larspontoppidan/midimixfix/HW/Misc/foot_pedal_cct_new.GIF

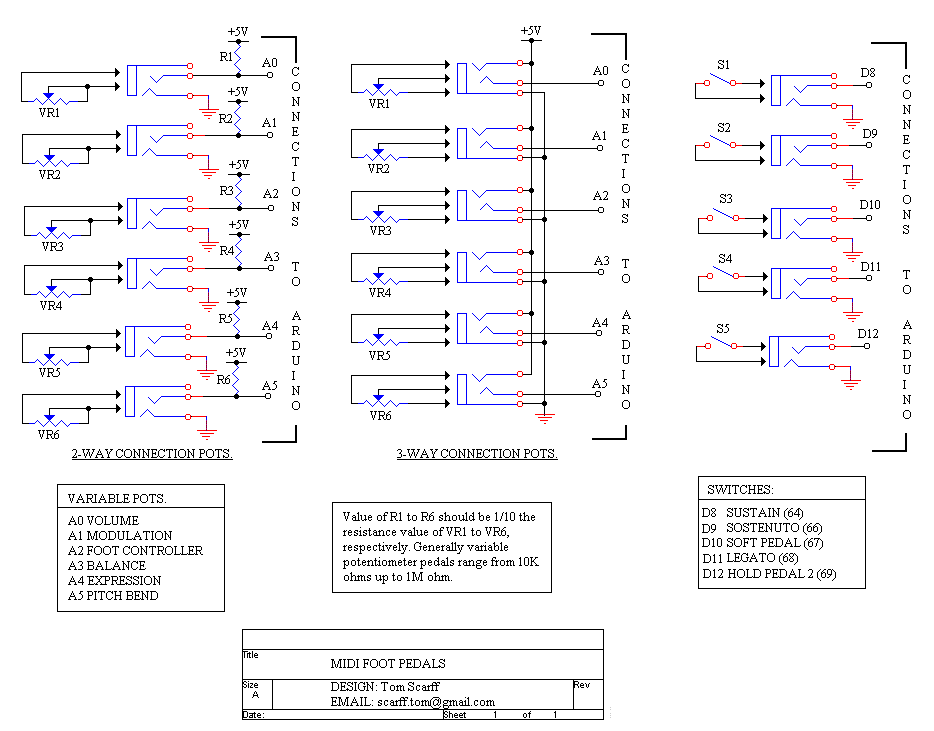
HW/Misc/foot_pedal_cct_new.GIF
