larspontoppidan/midimixfix/Releases/HW Release Rev 1/Pictures/Midimixfix mounted.JPG

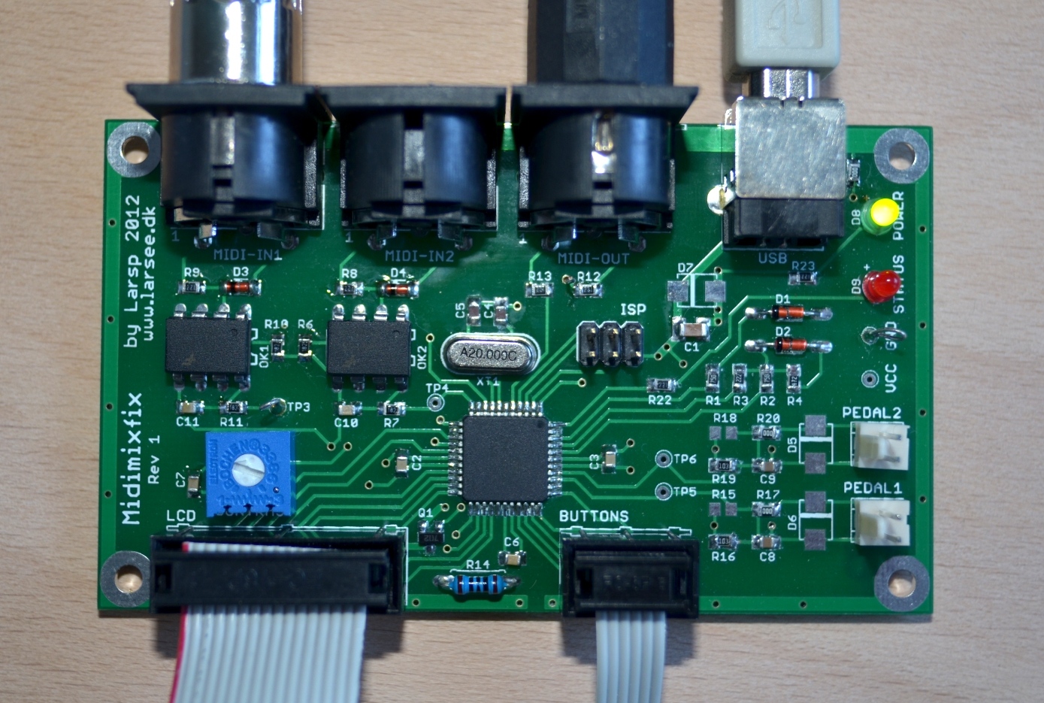
Releases/HW Release Rev 1/Pictures/Midimixfix mounted.JPG
