larspontoppidan/midimixfix/Releases/HW Release Rev 1/Pictures/Midimixfix PCB Back.JPG

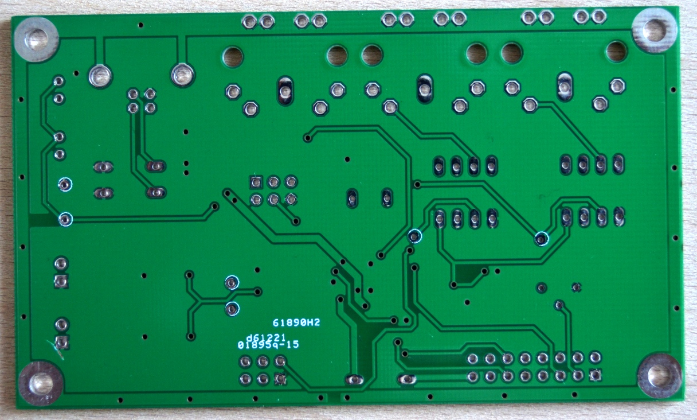
Releases/HW Release Rev 1/Pictures/Midimixfix PCB Back.JPG
