larspontoppidan/midimixfix/Releases/HW Release Rev 1/Pictures/Midimixfix PCB Front.JPG

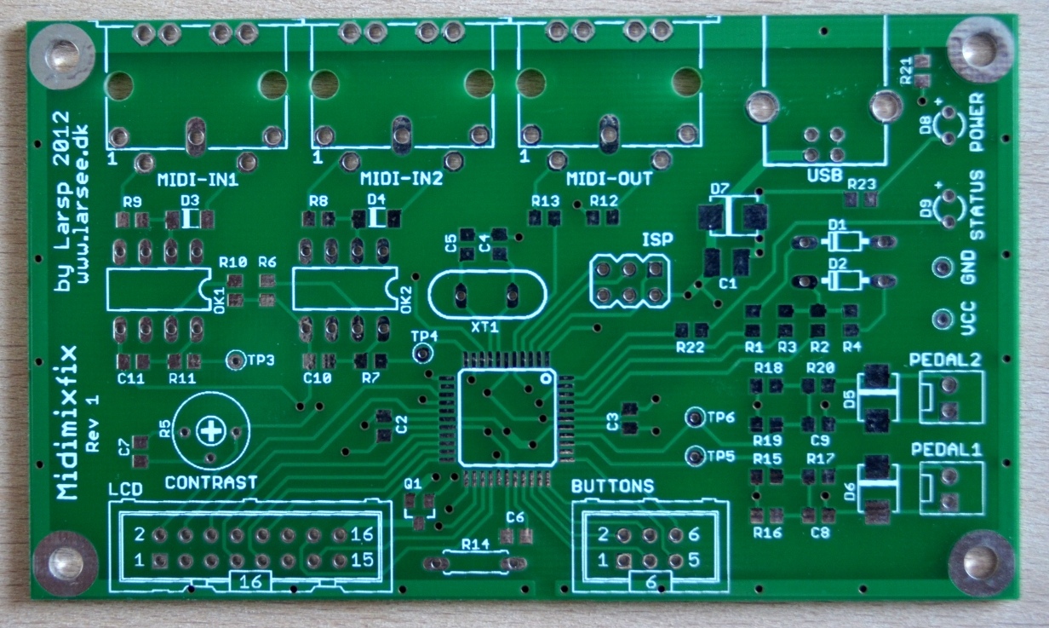
Releases/HW Release Rev 1/Pictures/Midimixfix PCB Front.JPG
