larspontoppidan/midimixfix/Releases/HW Release Rev 1/Pictures/Midimixfix prototype.JPG

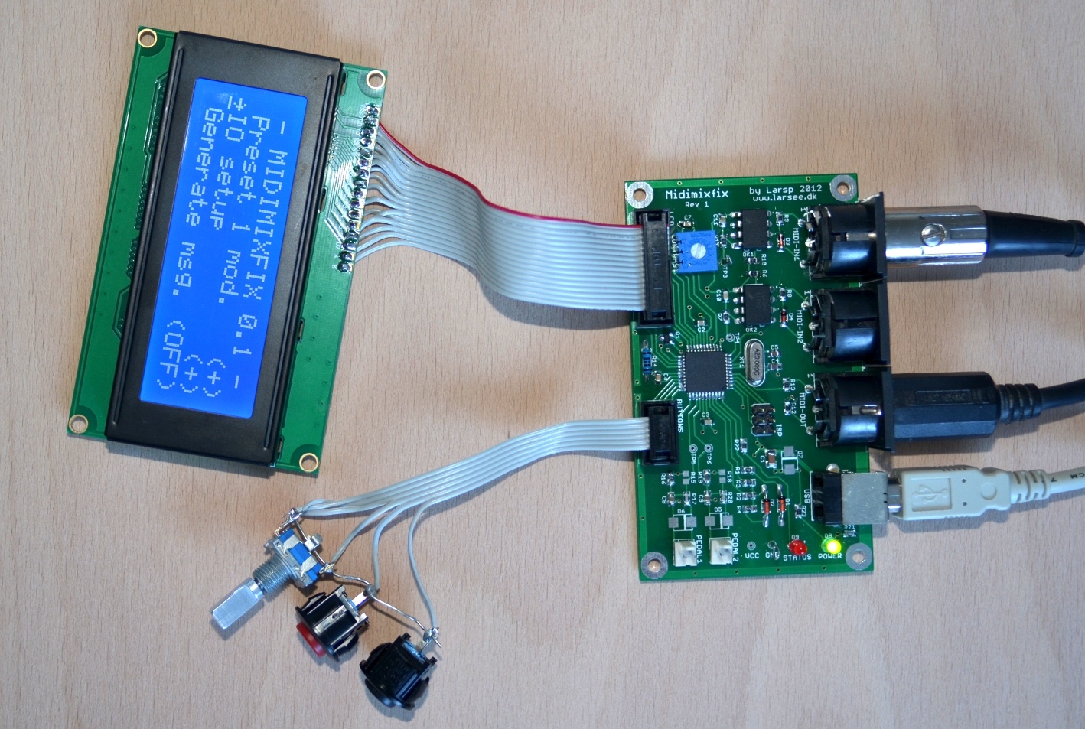
Releases/HW Release Rev 1/Pictures/Midimixfix prototype.JPG
