larspontoppidan/midimixfix/HW/Components/JACK receptacle/B1.JPG

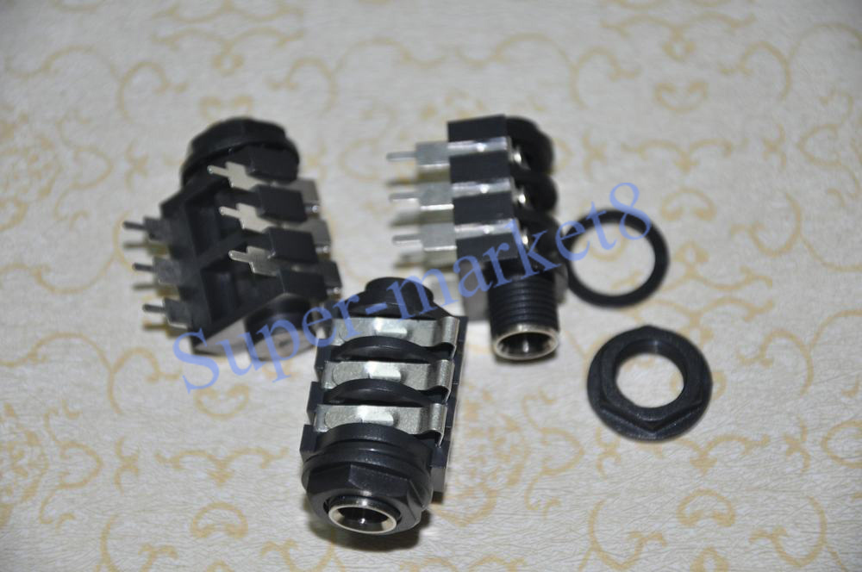
HW/Components/JACK receptacle/B1.JPG
