larspontoppidan/midimixfix/HW/Components/LCD Module/2004-lcd-module.jpg

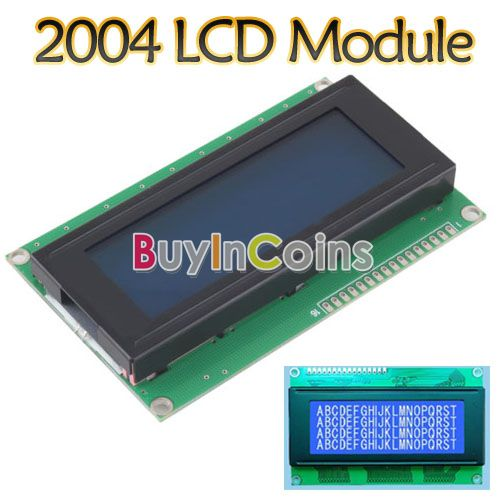
HW/Components/LCD Module/2004-lcd-module.jpg
