larspontoppidan/midimixfix/HW/Components/LCD Module/2004-lcd-module_03.jpg

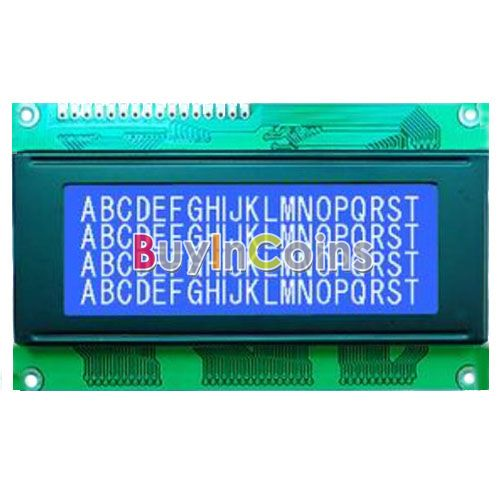
HW/Components/LCD Module/2004-lcd-module_03.jpg
