larspontoppidan/midimixfix/HW/Components/LCD Module/2004-lcd-module_05.jpg

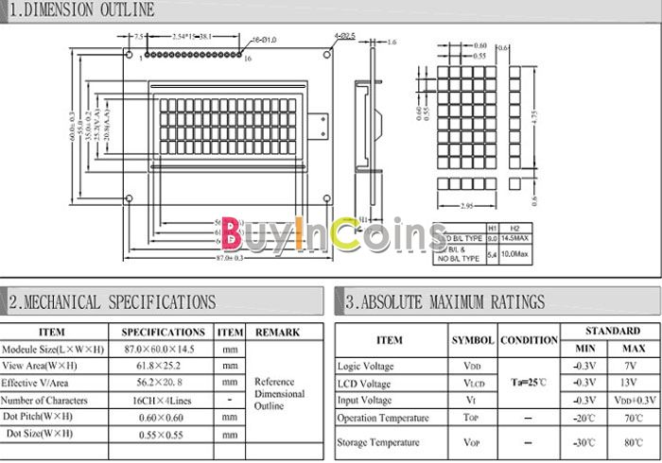
HW/Components/LCD Module/2004-lcd-module_05.jpg
