larspontoppidan/midimixfix/HW/Components/Rotary encoder/14002056_1_image_59740.jpg

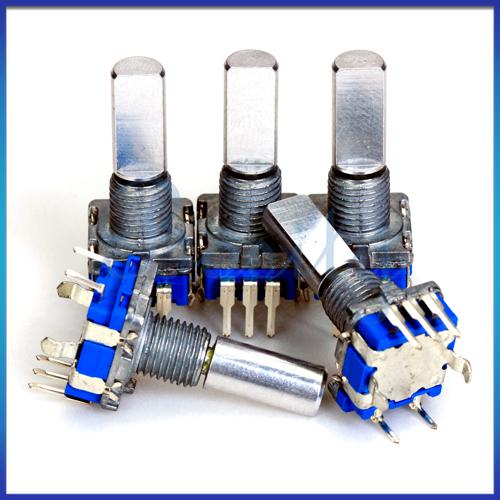
HW/Components/Rotary encoder/14002056_1_image_59740.jpg
