larspontoppidan/midimixfix/Releases/HW Release Rev 1/Cable assembly/Midimixfix_into_box_012-1024x678.jpg

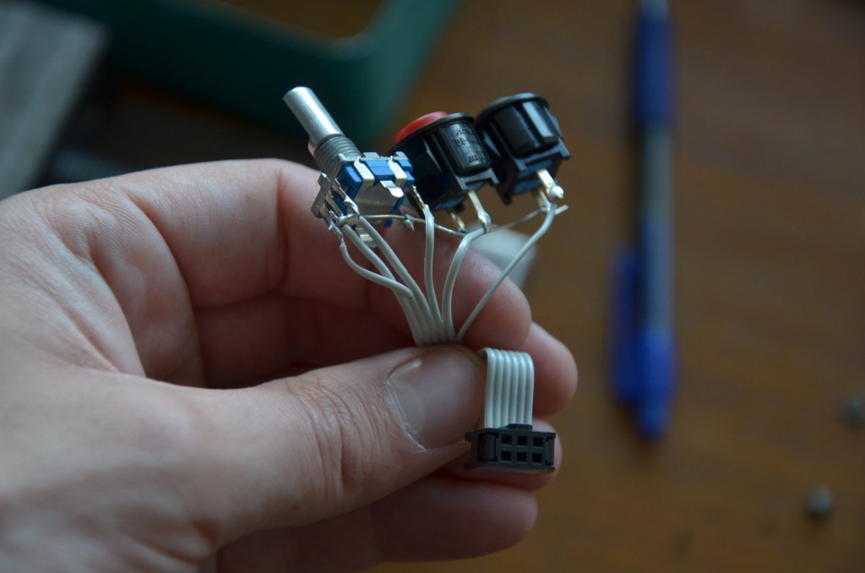
Releases/HW Release Rev 1/Cable assembly/Midimixfix_into_box_012-1024x678.jpg
