larspontoppidan/midimixfix/SW/src/Filters/controlnoteon.h

/*
 * controlnoteon.h
 *
 *  Created on: May 16, 2014
 *      Author: lars
 */

#ifndef CONTROLNOTEON_H_
#define CONTROLNOTEON_H_



#include "../common.h"
#include "../filterinterface.h"
#include <avr/pgmspace.h>

extern const filterInterface_t PROGMEM ccnoteon_Filter;



#endif /* CONTROLNOTEON_H_ */
