larspontoppidan/midimixfix/SW/src/Filters/modifycontroller.h

/*
 * modifycontroller.h
 *
 *  Created on: Oct 18, 2013
 *      Author: lars
 */

#ifndef MODIFYCONTROLLER_H_
#define MODIFYCONTROLLER_H_


#include "../common.h"
#include "../filterinterface.h"
#include <avr/pgmspace.h>

extern const filterInterface_t PROGMEM modifycc_Filter;


#endif /* MODIFYCONTROLLER_H_ */
