larspontoppidan/midimixfix/SW/src/Filters/pedals.c

//
// Filename    : pedals.c
// Code module : Generation of midi messages from pedal readings for MidiMixFix
// Project     : Midimixfix
// URL         : http://larsee.dk
//
// --------------------------------  LICENSE  -----------------------------------
//
// Copyright (c) 2013, Lars Ole Pontoppidan (Larsp)
// All rights reserved.
//
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
// THIS SOFTWARE IS PROVIDED BY THE COPYRIGHT HOLDERS AND CONTRIBUTORS "AS IS" AND
// ANY EXPRESS OR IMPLIED WARRANTIES, INCLUDING, BUT NOT LIMITED TO, THE IMPLIED
// WARRANTIES OF MERCHANTABILITY AND FITNESS FOR A PARTICULAR PURPOSE ARE
// DISCLAIMED. IN NO EVENT SHALL THE COPYRIGHT OWNER OR CONTRIBUTORS BE LIABLE FOR
// ANY DIRECT, INDIRECT, INCIDENTAL, SPECIAL, EXEMPLARY, OR CONSEQUENTIAL DAMAGES
// (INCLUDING, BUT NOT LIMITED TO, PROCUREMENT OF SUBSTITUTE GOODS OR SERVICES;
// LOSS OF USE, DATA, OR PROFITS; OR BUSINESS INTERRUPTION) HOWEVER CAUSED AND
// ON ANY THEORY OF LIABILITY, WHETHER IN CONTRACT, STRICT LIABILITY, OR TORT
// (INCLUDING NEGLIGENCE OR OTHERWISE) ARISING IN ANY WAY OUT OF THE USE OF THIS
// SOFTWARE, EVEN IF ADVISED OF THE POSSIBILITY OF SUCH DAMAGE.
//
//
//
// ------------------------------  DESCRIPTION  ---------------------------------


// -------------------------------  INCLUDES  -----------------------------------
/*
 * pedals.c
 *
 *  Created on: May 11, 2013
 *      Author: lars
 */


#include "../common.h"
#include "../midimessage.h"
#include "../midigenerics.h"
#include "../midiprocessing.h"
#include "../errors.h"
#include "../util.h"
#include "../hal.h"
#include "../filters.h"
#include "../ui.h"
#include "../menus/filtermenu.h"
#include <avr/pgmspace.h>
#include "filteruids.h"

// DATA PROCESSING
//
// A variable pedal is sampled by midimixfix using a voltage divider into a 10-bit ADC:
//
//   VCC ---+
//          |
//         10k
//          |
//          +----  ADC
//          |
//       R_pedal
//          |
//   GND ---+
//
// The circuit maps the pedal resistance non-linearly to the voltage seen by the ADC:
//
//   V_ADC = VCC * R_pedal / (10k + R_pedal)
//
// If we want to derive the actual R_pedal value without the non-linearity, we need to find:
//
//   R_pedal = 10 * V_ADC / (VCC - V_ADC)
//
// To calculate R_pedal using above formula, a look up table is used. The table simply has
// one 16-bit entry for each possible ADC value, and is scaled to have unit 1/64 ohms.
// The scaling is selected to enable a convenient gain calculation followed by >> 8.
//
// Python to generate the table:
//
// from numpy import *
//
// a = range(1024)
//
// for i in xrange(1000):
//   a[i] = int(round(10000.0 / 64.0 * (i/1024.0) / (1.0-(i/1024.0))))
//
// array(a).reshape(-1,8)


// ------------------------------  PROTOTYPES  ----------------------------------


static uint8_t ProcessAdcValue(int8_t offset, uint8_t gain, uint16_t adc_value);
static uint8_t handleDigitalPedal_ISR(uint8_t p);
static uint8_t handleAnalogPedal_ISR(uint8_t p);

static uint8_t pedals_In1Create(uint8_t filter_step);
static uint8_t pedals_In2Create(uint8_t filter_step);
static void pedals_Destroy(uint8_t instance);
static void pedals_SetFilterStep(uint8_t instance, uint8_t filter_step);
static void pedals_LoadConfig(uint8_t instance, void* data);
static void pedals_SaveConfig(uint8_t instance, void* data);
static uint8_t pedals_ProcessMidiMsgNull(uint8_t instance, midiMsg_t *msg);
static void pedals_WriteMenuText(uint8_t instance, uint8_t menu_item, void *dest);
static void pedals_HandleUiEvent(uint8_t instance, uint8_t menu_item, uint8_t ui_event);

// --------------------------  TYPES AND CONSTANTS  -----------------------------

#define GAIN_USE_DIGITAL      0

#define USE_MIDI_CHANNEL 0

#define DIGITAL_HIGH_TRIGGER  683u  // 2/3 of full ADC gain
#define DIGITAL_LOW_TRIGGER   341u  // 1/3 of full ADC gain

#define ANALOG_STICKY 1

#define INVERT_TABLE_MAX 1024


typedef struct
{
    uint8_t  Gain;
    int8_t  Offset;
    uint8_t Controller;
    bool_t  Inverted;
} pedalSetup_t;

typedef struct
{
    bool_t InUse;  // True if this pedal is active as a filter
    uint8_t FilterStep;
    uint8_t State; // The state of the digital / analog processing
    uint8_t Value; // The latest output value for this pedal
} pedalState_t;

static uint16_t const InvertTable[INVERT_TABLE_MAX] PROGMEM =
{
       0u,   0u,   0u,   0u,   1u,   1u,   1u,   1u,
       1u,   1u,   2u,   2u,   2u,   2u,   2u,   2u,
       2u,   3u,   3u,   3u,   3u,   3u,   3u,   4u,
       4u,   4u,   4u,   4u,   4u,   5u,   5u,   5u,
       5u,   5u,   5u,   6u,   6u,   6u,   6u,   6u,
       6u,   7u,   7u,   7u,   7u,   7u,   7u,   8u,
       8u,   8u,   8u,   8u,   8u,   9u,   9u,   9u,
       9u,   9u,   9u,  10u,  10u,  10u,  10u,  10u,
      10u,  11u,  11u,  11u,  11u,  11u,  11u,  12u,
      12u,  12u,  12u,  12u,  13u,  13u,  13u,  13u,
      13u,  13u,  14u,  14u,  14u,  14u,  14u,  15u,
      15u,  15u,  15u,  15u,  15u,  16u,  16u,  16u,
      16u,  16u,  17u,  17u,  17u,  17u,  17u,  17u,
      18u,  18u,  18u,  18u,  18u,  19u,  19u,  19u,
      19u,  19u,  20u,  20u,  20u,  20u,  20u,  21u,
      21u,  21u,  21u,  21u,  22u,  22u,  22u,  22u,
      22u,  23u,  23u,  23u,  23u,  23u,  24u,  24u,
      24u,  24u,  24u,  25u,  25u,  25u,  25u,  25u,
      26u,  26u,  26u,  26u,  26u,  27u,  27u,  27u,
      27u,  27u,  28u,  28u,  28u,  28u,  29u,  29u,
      29u,  29u,  29u,  30u,  30u,  30u,  30u,  30u,
      31u,  31u,  31u,  31u,  32u,  32u,  32u,  32u,
      32u,  33u,  33u,  33u,  33u,  34u,  34u,  34u,
      34u,  34u,  35u,  35u,  35u,  35u,  36u,  36u,
      36u,  36u,  37u,  37u,  37u,  37u,  37u,  38u,
      38u,  38u,  38u,  39u,  39u,  39u,  39u,  40u,
      40u,  40u,  40u,  41u,  41u,  41u,  41u,  42u,
      42u,  42u,  42u,  43u,  43u,  43u,  43u,  44u,
      44u,  44u,  44u,  45u,  45u,  45u,  45u,  46u,
      46u,  46u,  46u,  47u,  47u,  47u,  47u,  48u,
      48u,  48u,  48u,  49u,  49u,  49u,  49u,  50u,
      50u,  50u,  50u,  51u,  51u,  51u,  52u,  52u,
      52u,  52u,  53u,  53u,  53u,  53u,  54u,  54u,
      54u,  55u,  55u,  55u,  55u,  56u,  56u,  56u,
      57u,  57u,  57u,  57u,  58u,  58u,  58u,  59u,
      59u,  59u,  59u,  60u,  60u,  60u,  61u,  61u,
      61u,  61u,  62u,  62u,  62u,  63u,  63u,  63u,
      64u,  64u,  64u,  64u,  65u,  65u,  65u,  66u,
      66u,  66u,  67u,  67u,  67u,  68u,  68u,  68u,
      68u,  69u,  69u,  69u,  70u,  70u,  70u,  71u,
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
};


static const char In1Title[]     PROGMEM = "Pedal 1";
static const char In2Title[]     PROGMEM = "Pedal 2";
static const char DynamicTitle[] PROGMEM = " ->%i";

static const char SettingUiCc[]    PROGMEM = "CC.    : %C";
static const char SettingGain[]    PROGMEM = "Gain   : ";
static const char SettingOffset[]  PROGMEM = "Offset : %i";
static const char SettingInvert[]  PROGMEM = "Invert : %o";
static const char SettingDigital[] PROGMEM = "DIGITAL";

const filterInterface_t pedals_In1 PROGMEM =
{
        pedals_In1Create,
        pedals_Destroy,
        pedals_SetFilterStep,
        pedals_LoadConfig,
        pedals_SaveConfig,
        pedals_ProcessMidiMsgNull,
        pedals_WriteMenuText,
        pedals_HandleUiEvent,

        sizeof(pedalSetup_t),  // Number of bytes in configuration
        4,                     // Number of menu items (0 means only title, 1 is one item)
        9,                     // Cursor indentation in menu
        FILTER_MODE_OUT,       // Filter operation mode
        In1Title,              // Static filter title (this may be different from in-menu title)

        FILTER_UID(FILTER_ID_PEDALS_IN1, 1)
};

const filterInterface_t pedals_In2 PROGMEM =
{
        pedals_In2Create,
        pedals_Destroy,
        pedals_SetFilterStep,
        pedals_LoadConfig,
        pedals_SaveConfig,
        pedals_ProcessMidiMsgNull,
        pedals_WriteMenuText,
        pedals_HandleUiEvent,

        sizeof(pedalSetup_t),  // Number of bytes in configuration
        4,                     // Number of menu items (0 means only title, 1 is one item)
        9,                     // Cursor indentation in menu
        FILTER_MODE_OUT,       // Filter operation mode
        In2Title,              // Static filter title (this may be different from in-menu title)

        FILTER_UID(FILTER_ID_PEDALS_IN2, 1)
};

// -------------------------------  VARIABLES  ----------------------------------

static pedalSetup_t PedalSetup[2];
static pedalState_t PedalState[2];

static bool_t UpdatePedal1;
static bool_t UpdatePedal2;

// ------------------------  MIDI FILTER INTERFACE FUNCTIONS  -------------------

static uint8_t pedals_In1Create(uint8_t filter_step)
{
    uint8_t ret = FILTER_CREATE_FAILED;

    if (PedalState[0].InUse == FALSE)
    {
        PedalState[0].InUse = TRUE;
        PedalState[0].FilterStep = filter_step;

        ret = 0; // Return instance number for Pedal1, which is 0
    }

    return ret;
}

static uint8_t pedals_In2Create(uint8_t filter_step)
{
    uint8_t ret = FILTER_CREATE_FAILED;

    if (PedalState[1].InUse == FALSE)
    {
        PedalState[1].InUse = TRUE;
        PedalState[1].FilterStep = filter_step;
        ret = 1; // Return instance number for Pedal2, which is 1
    }

    return ret;
}

static void pedals_Destroy(uint8_t instance)
{
    PedalState[instance].InUse = FALSE;
}

static void pedals_SetFilterStep(uint8_t instance, uint8_t filter_step)
{
    PedalState[instance].FilterStep = filter_step;
}

static void pedals_LoadConfig(uint8_t instance, void* data)
{
    PedalSetup[instance] = *((pedalSetup_t*)data);
}

static void pedals_SaveConfig(uint8_t instance, void* data)
{
    *((pedalSetup_t*)data) = PedalSetup[instance];
}

static uint8_t pedals_ProcessMidiMsgNull(uint8_t instance, midiMsg_t *msg)
{
    (void)(instance);
    (void)(msg);
    return 0;
}

static void pedals_WriteMenuText(uint8_t instance, uint8_t menu_item, void *dest)
{
    switch (menu_item)
    {
    case 0: // Write dynamic title including the actual output value of filter
        dest = util_copyString_P(dest, (instance == 0) ? In1Title : In2Title);
        util_writeFormat_P(dest, DynamicTitle, PedalState[instance].Value);
        break;

    case 1: // Set controller menu item
        util_writeFormat_P(dest, SettingUiCc, PedalSetup[instance].Controller);
        break;

    case 2:
        dest = util_copyString_P(dest, SettingGain);
        if (PedalSetup[instance].Gain == GAIN_USE_DIGITAL)
        {
            util_copyString_P(dest, SettingDigital);
        }
        else
        {
            util_writeUint8(dest, PedalSetup[instance].Gain);
        }
        break;
    case 3:
        util_writeFormat_P(dest, SettingOffset, PedalSetup[instance].Offset);
        break;
    case 4:
        util_writeFormat_P(dest, SettingInvert, PedalSetup[instance].Inverted);
        break;
    }

}


static void pedals_HandleUiEvent(uint8_t instance, uint8_t menu_item, uint8_t ui_event)
{
    int8_t delta = ui_eventToDelta(ui_event, 10);

    switch (menu_item)
    {
    case 1:
        PedalSetup[instance].Controller =
            util_boundedAddUint8(PedalSetup[instance].Controller, 0, MIDI_UICC_COUNT - 1, delta);
        break;

    case 2:
        PedalSetup[instance].Gain =
             util_boundedAddUint8(PedalSetup[instance].Gain, 0, 255, delta);
        break;

    case 3:
        PedalSetup[instance].Offset =
             util_boundedAddInt8(PedalSetup[instance].Offset, -128, 127, delta);
        break;
    case 4:
        PedalSetup[instance].Inverted = ui_eventToSetClearBit(ui_event, PedalSetup[instance].Inverted, 1);
        break;
    }
}

// ---------------------------  PRIVATE FUNCTIONS  ------------------------------

static uint8_t ProcessAdcValue(int8_t offset, uint8_t gain, uint16_t adc_value)
{
    uint16_t x;

    // First look up adc_value in invert table:
    if (adc_value < INVERT_TABLE_MAX)
    {
        x = pgm_read_word(&(InvertTable[adc_value]));
    }
    else
    {
        x = 65535u;
    }

    // Perform gain calculation in 32 bit domain:

    //x = (uint16_t) (((uint32_t)x * (uint32_t)gain) >> 13);   // 11.52 us
    x = (uint16_t) (((uint32_t)x * (uint32_t)gain) >> 8);      // 7.24 us for entire function

    // Add offset in 16 bit signed domain:
    int16_t s;

    s = ((int16_t)x) + (int16_t)(offset);

    // Truncate to 0:127 and we are done
    if (s < 0)
    {
        return 0;
    }
    else if (s > 127)
    {
        return 127;
    }
    else
    {
        return (uint8_t)s;
    }
}


// The digital pedal processing includes a schmitt triggering function of the ADC value
static uint8_t handleDigitalPedal_ISR(uint8_t p)
{
    uint16_t value = hal_adcGetValue_ISR(p);

    // Implement 1/3, 2/3 schmitt trigger digital mode
    if (PedalState[p].State < 64)
    {
        PedalState[p].State = (value < DIGITAL_HIGH_TRIGGER) ? 0 : 127;
    }
    else
    {
        PedalState[p].State = (value < DIGITAL_LOW_TRIGGER) ? 0 : 127;
    }

    if (PedalSetup[p].Inverted)
    {
        return 127 - PedalState[p].State;
    }
    else
    {
        return PedalState[p].State;
    }
}

// The analog processing first transforms the ADC value including gain / offset.
// The processed value is compared to the last value and a "sticky" algorithm checks
// if the new value should be adopted or not. The purpose is to avoid unnecessary midi
// transmissions toggling back and forth between two adjacent controller values.
static uint8_t handleAnalogPedal_ISR(uint8_t p)
{
    uint8_t new_value;
    uint8_t state;
    int8_t diff;

    // Apply gain / offset analog transformation
    new_value = ProcessAdcValue(PedalSetup[p].Offset, PedalSetup[p].Gain, hal_adcGetValue_ISR(p));

    // CurrentState encode the last value, and if we are considered stable:
    state = PedalState[p].State;

    diff = (int8_t)new_value - (int8_t)(state & 127u);

    if (diff == 0)
    {
        // No change, make sure stable flag is set
        state |= 128;
    }
    else
    {
        if (state & 128)
        {
            // There is a change, and we are supposed to be stable, is change large enough?

            if (diff < 0)
            {
                diff = -diff;
            }

            if (diff > ANALOG_STICKY)
            {
                // Yes. Set new state and don't set stable bit
                state = new_value;
            }
            else
            {
                // Change not large enough. Don't do anything.
            }
        }
        else
        {
            // We are not stable, simply adopt new value
            state = new_value;
        }
    }

    // Write back new state
    PedalState[p].State = state;

    if (PedalSetup[p].Inverted)
    {
        return 127 - (state & 127);
    }
    else
    {
        return (state & 127);
    }
}

// ---------------------------  PUBLIC FUNCTIONS  -------------------------------

void pedals_initialize(void)
{
    // Set some usable defaults
    PedalSetup[0].Controller = 4;  // Volume
    PedalSetup[0].Inverted = TRUE;
    PedalSetup[0].Gain = 50;
    PedalSetup[0].Offset = -1;

    PedalSetup[1].Controller = 10; // SustainP.
    PedalSetup[1].Inverted = TRUE;
    PedalSetup[1].Gain = 0;
    PedalSetup[1].Offset = 0;
}

void pedals_handleTick_ISR(void)
{
    uint8_t new_value;

    if (PedalState[0].InUse)
    {
        if (PedalSetup[0].Gain == GAIN_USE_DIGITAL)
        {
            new_value = handleDigitalPedal_ISR(0);
        }
        else
        {
            new_value = handleAnalogPedal_ISR(0);
        }

        if (new_value != PedalState[0].Value)
        {
            PedalState[0].Value = new_value;

            // Generate midi message
            midiMsg_t msg;
            midimsg_newContinuousCtrl(&msg, USE_MIDI_CHANNEL,
                    midi_convertUiccToCc(PedalSetup[0].Controller), new_value);
            midiproc_addMessage_ISR(&msg, PedalState[0].FilterStep);

            // Notify that we may want to update this in menu
            UpdatePedal1 = TRUE;
        }


    }

    if (PedalState[1].InUse)
    {
        if (PedalSetup[1].Gain == GAIN_USE_DIGITAL)
        {
            new_value = handleDigitalPedal_ISR(1);
        }
        else
        {
            new_value = handleAnalogPedal_ISR(1);
        }

        if (new_value != PedalState[1].Value)
        {
            PedalState[1].Value = new_value;

            // Generate midi message
            midiMsg_t msg;
            midimsg_newContinuousCtrl(&msg, USE_MIDI_CHANNEL,
                    midi_convertUiccToCc(PedalSetup[1].Controller), new_value);
            midiproc_addMessage_ISR(&msg, PedalState[1].FilterStep);

            // Notify that we may want to update this in menu
            UpdatePedal2 = TRUE;
        }

    }

    // Profiling. Analog pedal processing, min: 9.6 us, max: 31.6 us   (before restructuring!)
    // Profiling. Digital pedal processing, min: 4.8 us, max: 26.4 us  (before restructuring!)

}

void pedals_handleMainLoop(void)
{
    if (UpdatePedal1)
    {
        UpdatePedal1 = FALSE;

        // Build our instance
        filters_instance_t instance;
        instance.FilterType = FILTER_TYPE_PEDALS_IN1;
        instance.Instance = 0;

        // Request update of menu title
        filtermenu_RequestUpdate(instance, 0);
    }

    if (UpdatePedal2)
    {
        UpdatePedal2 = FALSE;

        // Build our instance
        filters_instance_t instance;
        instance.FilterType = FILTER_TYPE_PEDALS_IN2;
        instance.Instance = 1;

        // Request update of menu title
        filtermenu_RequestUpdate(instance, 0);

    }
}
