larspontoppidan/midimixfix/SW/src/Filters/curvemath.c

/*
 * curvemath.c
 *
 *  Created on: Jan 12, 2013
 *      Author: lars
 */


#include "../common.h"
#include "curvemath.h"
#include "../util.h"
#include "avr/pgmspace.h"

// Curve type names

static char const CurveNames[CURVEMATH_TYPES][10] PROGMEM =
{
    {"Linear"},  // 0
    {"Gamma 0.6"},  // 1
    {"Gamma 0.8"},  // 2
    {"Gamma 1.2"},  // 3
    {"Gamma 1.6"},  // 4
    {"-S- shape"},  // 5
    {"-N- shape"},  // 6
};

#define GAIN_FIXPOINT_SCALE  64





// Curves
/////////////////

// Python example to generate the linear table:
//
// from numpy import *
//
// a = range(128)
//
// for i in xrange(128):
//    a[i] = i * 2
//
// array(a).reshape(-1,8)


static uint8_t const CurveTables[CURVEMATH_TYPES][128] PROGMEM =
{
    // Linear
    {   0,   2,   4,   6,   8,  10,  12,  14,
       16,  18,  20,  22,  24,  26,  28,  30,
       32,  34,  36,  38,  40,  42,  44,  46,
       48,  50,  52,  54,  56,  58,  60,  62,
       64,  66,  68,  70,  72,  74,  76,  78,
       80,  82,  84,  86,  88,  90,  92,  94,
       96,  98, 100, 102, 104, 106, 108, 110,
      112, 114, 116, 118, 120, 122, 124, 126,
      128, 130, 132, 134, 136, 138, 140, 142,
      144, 146, 148, 150, 152, 154, 156, 158,
      160, 162, 164, 166, 168, 170, 172, 174,
      176, 178, 180, 182, 184, 186, 188, 190,
      192, 194, 196, 198, 200, 202, 204, 206,
      208, 210, 212, 214, 216, 218, 220, 222,
      224, 226, 228, 230, 232, 234, 236, 238,
      240, 242, 244, 246, 248, 250, 252, 254
    },

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
     202, 204, 206, 207, 209, 211, 212, 214,
     216, 217, 219, 220, 222, 223, 225, 226,
     227, 229, 230, 231, 233, 234, 235, 236,
     237, 239, 240, 241, 242, 243, 244, 245,
     246, 247, 247, 248, 249, 250, 250, 251,
     252, 252, 253, 253, 253, 254, 254, 254
    },

    // Arctan S curve:
    //   a[i] = int(round((arctan(i/127.0*4-2)+arctan(2))/arctan(2)/2 * 254))
    // (The formula scales arctan(-2 ... 2) curve to fit this purpose)
    {
       0,   1,   1,   2,   3,   4,   5,   6,
       6,   7,   8,   9,  10,  11,  12,  13,
      14,  16,  17,  18,  19,  20,  22,  23,
      24,  26,  27,  29,  31,  32,  34,  36,
      37,  39,  41,  43,  45,  47,  49,  52,
      54,  56,  59,  61,  64,  66,  69,  72,
      75,  78,  81,  84,  87,  90,  94,  97,
     100, 104, 107, 111, 114, 118, 122, 125,
     129, 132, 136, 140, 143, 147, 150, 154,
     157, 160, 164, 167, 170, 173, 176, 179,
     182, 185, 188, 190, 193, 195, 198, 200,
     202, 205, 207, 209, 211, 213, 215, 217,
     218, 220, 222, 223, 225, 227, 228, 230,
     231, 232, 234, 235, 236, 237, 238, 240,
     241, 242, 243, 244, 245, 246, 247, 248,
     248, 249, 250, 251, 252, 253, 253, 254
    },

    // Tangens curve:
    //  a[i] = int(round((tan(i/127.0*2.2-1.1)+tan(1.1))/tan(1.1)/2 * 254))
    // (The formula scales tan(-1.1 ... 1.1) curve to fit this purpose)
    {
       0,   5,  10,  15,  19,  23,  27,  31,
      34,  38,  41,  44,  47,  50,  52,  55,
      57,  60,  62,  64,  66,  68,  70,  72,
      74,  76,  78,  80,  81,  83,  85,  86,
      88,  89,  91,  92,  94,  95,  96,  98,
      99, 100, 102, 103, 104, 106, 107, 108,
     109, 110, 112, 113, 114, 115, 116, 117,
     119, 120, 121, 122, 123, 124, 125, 126,
     128, 129, 130, 131, 132, 133, 134, 135,
     137, 138, 139, 140, 141, 142, 144, 145,
     146, 147, 148, 150, 151, 152, 154, 155,
     156, 158, 159, 160, 162, 163, 165, 166,
     168, 169, 171, 173, 174, 176, 178, 180,
     182, 184, 186, 188, 190, 192, 194, 197,
     199, 202, 204, 207, 210, 213, 216, 220,
     223, 227, 231, 235, 239, 244, 249, 254
    }
};




// PRIVATE


// Calculate the high value without truncation for user display
int16_t curvem_CalculateHigh(int16_t gain, int8_t offset)
{
    int16_t w;

    // Apply gain on maximum value
    w = ((int16_t)254) * gain;

    // Gain is a fix-point number with scaling factor GAIN_FIXPOINT_SCALE
    // The curve lookup also has scaling a factor: 2

    // Convert back to normal scale
    w = w / (GAIN_FIXPOINT_SCALE*2);

    // Add offset
    w += offset;

    return w;
}

// PUBLIC

void curvemath_reset(curveMath_t *curve)
{
    curve->Type = 0;
    curve->Gain = GAIN_FIXPOINT_SCALE;
    curve->Offset = 0;
}

// Functions for displaying the curve spec
char *curvemath_writeLow(char *dest, curveMath_t *curve)
{
    return util_writeInt8LA(dest, curve->Offset);
}

char *curvemath_writeType(char *dest, curveMath_t *curve)
{
    return util_copyString_P(dest, CurveNames[curve->Type]);
}

char *curvemath_writeHigh(char *dest, curveMath_t *curve)
{
    int16_t high = curvem_CalculateHigh(curve->Gain, curve->Offset);

    return util_writeInt16LA(dest, high);
}

// Applying curve on a value
uint8_t curvemath_apply(uint8_t x, curveMath_t *curve)
{
    uint8_t ret;
    int16_t w;

    // Non-linear curve look up
    x = pgm_read_byte(&(CurveTables[curve->Type][x]));

    // Apply gain on x
    w = ((int16_t)x) * (curve->Gain);

    // Gain is a fix-point number with scaling factor GAIN_FIXPOINT_SCALE
    // The curve lookup also has scaling a factor: 2

    // Convert back to normal scale
    //w = w / (GAIN_FIXPOINT_SCALE * 2);
    w >>= 7;

    // Add offset
    w += (int16_t)(curve->Offset);

    // Perform safe conversion to 7bit
    if (w > 127)
    {
        ret = 127;
    }
    else if (w < 0)
    {
        ret = 0;
    }
    else
    {
        ret = (uint8_t)w;
    }

    return ret;
}
