larspontoppidan/midimixfix/SW/src/Filters/conditionalroute.h

/*
 * conditionalroute.h
 *
 *  Created on: May 16, 2014
 *      Author: lars
 */

#ifndef CONDITIONALROUTE_H_
#define CONDITIONALROUTE_H_

#include "../common.h"
#include "../filterinterface.h"
#include <avr/pgmspace.h>

extern const filterInterface_t PROGMEM condroute_Filter;



#endif /* CONDITIONALROUTE_H_ */
