larspontoppidan/midimixfix/SW/src/Filters/keysplitroute.h

/*
 * keysplitroute.h
 *
 *  Created on: May 16, 2014
 *      Author: lars
 */

#ifndef KEYSPLITROUTE_H_
#define KEYSPLITROUTE_H_


#include "../common.h"
#include "../filterinterface.h"
#include <avr/pgmspace.h>

extern const filterInterface_t PROGMEM keysplit_Filter;



#endif /* KEYSPLITROUTE_H_ */
