larspontoppidan/midimixfix/SW/src/Filters/routeduplicate.h

/*
 * routeduplicate.h
 *
 *  Created on: Oct 18, 2013
 *      Author: lars
 */

#ifndef ROUTEDUPLICATE_H_
#define ROUTEDUPLICATE_H_



#include "../common.h"
#include "../filterinterface.h"
#include <avr/pgmspace.h>

extern const filterInterface_t PROGMEM dupmsg_Filter;
extern const filterInterface_t PROGMEM routemsg_Filter;

#endif /* ROUTEDUPLICATE_H_ */
