larspontoppidan/midimixfix/SW/src/Filters/routemsg.h

/*
 * routemsg.h
 *
 *  Created on: Oct 18, 2013
 *      Author: lars
 */

#ifndef ROUTEMSG_H_
#define ROUTEMSG_H_


#include "../common.h"
#include "../filterinterface.h"
#include <avr/pgmspace.h>

extern const filterInterface_t PROGMEM routemsg_Filter;

#endif /* ROUTEMSG_H_ */
