larspontoppidan/midimixfix/SW/src/Filters/setchannel.h

/*
 * setchannel.h
 *
 *  Created on: Oct 18, 2013
 *      Author: lars
 */

#ifndef SETCHANNEL_H_
#define SETCHANNEL_H_



#include "../common.h"
#include "../filterinterface.h"
#include <avr/pgmspace.h>

extern const filterInterface_t PROGMEM setchan_Filter;


#endif /* SETCHANNEL_H_ */
