larspontoppidan/midimixfix/SW/src/Filters/transposefilter.h

/*
 * transposefilter.h
 *
 *  Created on: Oct 18, 2013
 *      Author: lars
 */

#ifndef TRANSPOSEFILTER_H_
#define TRANSPOSEFILTER_H_


#include "../common.h"
#include "../filterinterface.h"
#include <avr/pgmspace.h>

extern const filterInterface_t PROGMEM transfilter_Filter;


#endif /* TRANSPOSEFILTER_H_ */
