larspontoppidan/midimixfix/SW/src/util.c

/*
 * stringutil.c
 *
 *  Created on: Dec 21, 2012
 *      Author: lars
 */

#include "common.h"
#include "util.h"
#include "pgmstrings.h"
#include "midimessage.h"
#include "midigenerics.h"

int16_t TenthsTab[5] = {10000, 1000, 100, 10, 1};

char *util_writeInt16(char *dest, int16_t value)
{
    uint8_t p;
    uint8_t c;

    bool_t numbernow = FALSE;

    if (value < 0)
    {
        *(dest++) = '-';
        value = -value;
    }
    else
    {
        *(dest++) = ' ';
    }

    for (p = 0; p < 5; p++)
    {
        if (value < TenthsTab[p])
        {
            if (numbernow || (p == 4))
            {
                *(dest++) = '0';
            }
            else
            {
                *(dest++) = ' ';
            }
        }
        else
        {
            c = '0';

            while (value >= TenthsTab[p])
            {
                c++;
                value -= TenthsTab[p];
            }

            *(dest++) = c;

            numbernow = 1;
        }
    }

    return dest;
}


char *util_writeInt16LA(char *dest, int16_t value)
{
    uint8_t p;
    uint8_t c;

    bool_t numbernow = FALSE;

    if (value < 0)
    {
        *(dest++) = '-';
        value = -value;
    }

    for (p = 0; p < 5; p++)
    {
        if (value < TenthsTab[p])
        {
            if (numbernow || (p == 4))
            {
                *(dest++) = '0';
            }
        }
        else
        {
            c = '0';

            while (value >= TenthsTab[p])
            {
                c++;
                value -= TenthsTab[p];
            }

            *(dest++) = c;

            numbernow = 1;
        }
    }

    return dest;
}


char * util_writeUint8(char *dest, uint8_t value)
{
    uint8_t c;
    bool_t numbernow = FALSE;

    c = 0u;
    while (value >= 100u)
    {
        c++;
        value -= 100u;
    }

    if (c != 0u)
    {
        *(dest++) = c + '0';
        numbernow = TRUE;
    }
    else
    {
        *(dest++) = ' ';
    }

    c = 0u;
    while (value >= 10u)
    {
        c++;
        value -= 10u;
    }

    if (numbernow || (c != 0u))
    {
        *(dest++) = c + '0';
    }
    else
    {
        *(dest++) = ' ';
    }

    *(dest++) = value + '0';

    return dest;
}


char *util_writeInt8LA(char *dest, int8_t x)
{
    uint8_t value;
    uint8_t c;

    bool_t numbernow = FALSE;

    if (x < 0)
    {
        *(dest++) = '-';
        value = (uint8_t)(-x);
    }
    else
    {
        value = (uint8_t)x;
    }

    c = 0u;
    while (value >= 100u)
    {
        c++;
        value -= 100u;
    }

    if (c != 0u)
    {
        *(dest++) = c + '0';
        numbernow = TRUE;
    }

    c = 0u;
    while (value >= 10u)
    {
        c++;
        value -= 10u;
    }

    if (numbernow || (c != 0u))
    {
        *(dest++) = c + '0';
    }

    *(dest++) = value + '0';

    return dest;
}

char *util_writeInt8(char *dest, int8_t x)
{
    uint8_t value;
    uint8_t c;

    bool_t numbernow = FALSE;

    if (x < 0)
    {
        *(dest++) = '-';
        value = (uint8_t)(-x);
    }
    else
    {
        *(dest++) = ' ';
        value = (uint8_t)x;
    }

    c = 0u;
    while (value >= 100u)
    {
        c++;
        value -= 100u;
    }

    if (c != 0u)
    {
        *(dest++) = c + '0';
        numbernow = TRUE;
    }
    else
    {
        *(dest++) = ' ';
    }

    c = 0u;
    while (value >= 10u)
    {
        c++;
        value -= 10u;
    }

    if (numbernow || (c != 0u))
    {
        *(dest++) = c + '0';
    }
    else
    {
        *(dest++) = ' ';
    }

    *(dest++) = value + '0';

    return dest;
}


char *util_writeHex(char *dest, uint8_t x)
{
    uint8_t c;

    c = (x >> 4);

    if (c <= 9)
    {
        *(dest++) = '0' + c;
    }
    else
    {
        *(dest++) = ('A' - 10) + c;
    }

    c = x & 15;

    if (c <= 9)
    {
        *(dest++) = '0' + c;
    }
    else
    {
        *(dest++) = ('A' - 10) + c;
    }

    return dest;
}


char *util_copyString_P(char *dest, PGM_P src)
{
    char c;

    while(1)
    {
        c = pgm_read_byte(src);

        if (c == 0u)
            break;

        *(dest++) = c;
        src++;
    }

    return dest;
}

char *util_copyString(char *dest, char *src)
{
    char c;

    while(1)
    {
        c = *src;

        if (c == 0u)
            break;

        *(dest++) = c;
        src++;
    }

    return dest;
}

int8_t util_boundedAddInt8(int8_t value, int8_t min, int8_t max, int8_t add)
{
    // Work in 16 bit signed space to avoid rollover
    int16_t x;

    x = (int16_t)value + (int16_t)add;

    if (x < (int16_t)min)
    {
        x = min;
    }
    else if (x > (int16_t)max)
    {
        x = max;
    }

    return (int8_t)x;
}

uint8_t util_boundedAddUint8(uint8_t value, uint8_t min, uint8_t max, int8_t add)
{
    // Work in 16 bit signed space to avoid rollover
    int16_t x;

    x = (int16_t)value + (int16_t)add;

    if (x < (int16_t)min)
    {
        x = min;
    }
    else if (x > (int16_t)max)
    {
        x = max;
    }

    return (uint8_t)x;
}


int16_t util_boundLimitInt16(int16_t value, int16_t min, int16_t max)
{
    if (value < min)
    {
        value = min;
    }
    else if (value > max)
    {
        value = max;
    }

    return value;
}

// Specialized function for writing right aligned component status
//
// Writes the following to dest[0] to dest[4]:
// "(OFF)"   value = 0
// "  (1)"   value = 1
// "  (2)"   value = 2
// " (10)"   value = 10
// "(200)"   value = 200

void util_writeNumberParentheses(char *dest, uint8_t value)
{
    if (value == 0)
    {
        util_copyString_P(dest, pstr_OffParentheses);
    }
    else
    {
        if (value < 10)
        {
            // One digit
            dest[0] = ' ';
            dest[1] = ' ';
            dest[2] = '(';
            dest[3] = value + '0';
        }
        else if (value < 100)
        {
            // Two digits
            dest[0] = ' ';
            dest[1] = '(';
            util_writeInt8LA(&(dest[2]), value);
        }
        else
        {
            // Three digits
            dest[0] = '(';
            util_writeInt16LA(&(dest[1]), (int16_t)value);
        }

        dest[4] = ')';
    }

}


// Write data from scr in dest until \0 is encountered
//
// Formatting specifiers in src will be used for writing the value from data
// in a certain way:
//
//   %U    Write data as uint8
//   %u    Write data as uint8 left adjusted
//   %I    Write data as int8
//   %i    Write data as int8 left adjusted
//   %x    Write data as hex
//   %O    Boolean written as " (ON)" or "(OFF)"
//   %o    Boolean written as "On" or "Off"
//   %y    Boolean written as "Yes" or "No"
//   %c    Write data as midi controller
//   %C    Write data as midi ui-controller
//   %n    Write data as note name "C#-4" for example
//
char *util_writeFormat_P(char *dest, PGM_P src, uint8_t data)
{
    bool_t finished = FALSE;
    char c;

    do
    {
        c = pgm_read_byte(src);
        src++;

        if (c == 0u)
        {
            finished = TRUE;
        }
        else if (c == '%')
        {
            c = pgm_read_byte(src);
            src++;

            switch (c)
            {
            case 'U':
                dest = util_writeUint8(dest, data);
                break;
            case 'u':
                dest = util_writeInt16LA(dest, (int16_t)data);
                break;
            case 'I':
                dest = util_writeInt8(dest, data);
                break;
            case 'i':
                dest = util_writeInt8LA(dest, data);
                break;
            case 'x':
                dest = util_writeHex(dest, data);
                break;
            case 'c':
                if (data == 0xFF)
                {
                    dest = util_copyString_P(dest, pstr_Off);
                }
                else
                {
                    dest = midi_writeControllerName(dest, data);
                }
                break;
            case 'C':
                dest = midi_writeUiccName(dest, data);
                break;
            case 'n':
                dest = midi_writeNoteName(dest, data);
                break;
            case 'O':
                dest = util_copyString_P(dest, data ? pstr_OnParentheses : pstr_OffParentheses);
                break;
            case 'y':
                dest = util_copyString_P(dest, data ? pstr_Yes : pstr_No);
                break;
            case 'o':
                dest = util_copyString_P(dest, data ? pstr_On : pstr_Off);
                break;
            case 0:
                finished = TRUE;
                break;
            default:
                *(dest++) = '%';
                *(dest++) = c;
                break;
            }
        }
        else
        {
            *(dest++) = c;
        }

    } while (finished == FALSE);

    return dest;
}


/*
 *
void lcd_WriteBin(uint8_t x)
{
    uint8_t i;

    for (i = 0; i < 8; i++)
    {
        if ((x & 0x80u) != 0u)
        {
            lcd_Write('1');
        }
        else
        {
            lcd_Write('0');
        }

        x = x * 2u;
    }
}

 */
