larspontoppidan/midimixfix/SW/src/ui.c

//
// Filename    : ui.c
// Code module : User interface (view and controller)
// Project     : Midimixfix
// URL         : http://larsee.dk
//
// --------------------------------  LICENSE  -----------------------------------
//
// Copyright (c) 2013, Lars Ole Pontoppidan (Larsp)
// All rights reserved.
//
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
// THIS SOFTWARE IS PROVIDED BY THE COPYRIGHT HOLDERS AND CONTRIBUTORS "AS IS" AND
// ANY EXPRESS OR IMPLIED WARRANTIES, INCLUDING, BUT NOT LIMITED TO, THE IMPLIED
// WARRANTIES OF MERCHANTABILITY AND FITNESS FOR A PARTICULAR PURPOSE ARE
// DISCLAIMED. IN NO EVENT SHALL THE COPYRIGHT OWNER OR CONTRIBUTORS BE LIABLE FOR
// ANY DIRECT, INDIRECT, INCIDENTAL, SPECIAL, EXEMPLARY, OR CONSEQUENTIAL DAMAGES
// (INCLUDING, BUT NOT LIMITED TO, PROCUREMENT OF SUBSTITUTE GOODS OR SERVICES;
// LOSS OF USE, DATA, OR PROFITS; OR BUSINESS INTERRUPTION) HOWEVER CAUSED AND
// ON ANY THEORY OF LIABILITY, WHETHER IN CONTRACT, STRICT LIABILITY, OR TORT
// (INCLUDING NEGLIGENCE OR OTHERWISE) ARISING IN ANY WAY OUT OF THE USE OF THIS
// SOFTWARE, EVEN IF ADVISED OF THE POSSIBILITY OF SUCH DAMAGE.
//

// ------------------------------  DESCRIPTION  ---------------------------------
//
// The ui module is first to process user interface events (knob turns, buttons)
//
//
// This module provides the overall menu roll up / down select, back functionality
// This functionality is used for all display screens, except for exclusive screens,
// such as midilog.
//
// Basically, a menu is something that can:
//   Draw a line on the screen (0 is top line, 3 is bottom)
//   Has a cursor concept
//   Handle user events
//
//


// The module implements a number of straightforward rolling menus, and can
// hand over the control of the user interface to another module, such as
// the filtermenu module.
//


// -------------------------------  INCLUDES  -----------------------------------

#include "ui.h"
#include "hal.h"
#include "common.h"
#include "util.h"
#include "lcd.h"
#include "errors.h"
#include "menuinterface.h"
#include "menus/mainmenu.h"

#include <avr/pgmspace.h>
#include <string.h>

// --------------------------  TYPES AND CONSTANTS  -----------------------------


#define REQUEST_ALL         0xFF
#define REQUEST_NONE        0
#define REQUEST_FIRST_ITEM  1

// ----------------------------  LOCAL VARIABLES  -------------------------------


// State:

static const menuInterface_t *Menu;

// Two levels of menu parent
static const menuInterface_t *MenuParent;
static const menuInterface_t *MenuParentParent;

static int8_t  MenuOffset;
static uint8_t RequestUpdate;

static uint8_t cursorCol;
static uint8_t cursorRow;


// ------------------------------  PROTOTYPES  ----------------------------------

static void writeBufferToLcd(uint8_t row, char *buffer);

static void writeAll(void);
static void writeMenuItem(uint8_t item);
static void drawCursor(void);

// Wrappers for accessing progmem stuff in menuInterface:
static inline bool_t  menuHasStaticTitle(const menuInterface_t *Menu);
static inline uint8_t menuInitGetCursor(const menuInterface_t *Menu);
static inline uint8_t menuGetItemCount(const menuInterface_t *Menu);
static inline void    menuWriteItem(const menuInterface_t *Menu, uint8_t item, char *dest);
static inline void    menuHandleUiEvent(const menuInterface_t *Menu, uint8_t uiEvent);

// --------------------------  PRIVATE FUNCTIONS  -------------------------------

static inline bool_t menuHasStaticTitle(const menuInterface_t *Menu)
{
    return (bool_t)(pgm_read_byte(&(Menu->hasStaticTitle)));
}

static inline uint8_t menuInitGetCursor(const menuInterface_t *Menu)
{
    fptrUint8Void_t initGetCursor = (fptrUint8Void_t)pgm_read_word(&(Menu->initGetCursor));
    return (initGetCursor)();
}

static inline uint8_t menuGetItemCount(const menuInterface_t *Menu)
{
    fptrUint8Void_t getItemCount = (fptrUint8Void_t)pgm_read_word(&(Menu->getItemCount));
    return (getItemCount)();
}

static inline void menuWriteItem(const menuInterface_t *Menu, uint8_t item, char *dest)
{
    fptrVoidUint8Voidp_t drawItem = (fptrVoidUint8Voidp_t)pgm_read_word(&(Menu->writeItem));
    (drawItem)(item, dest);
}

static inline void menuHandleUiEvent(const menuInterface_t *Menu, uint8_t uiEvent)
{
    fptrVoidUint8_t handleUiEvent = (fptrVoidUint8_t)pgm_read_word(&(Menu->handleUiEvent));
    (handleUiEvent)(uiEvent);
}



static void writeBufferToLcd(uint8_t row, char *buffer)
{
    uint8_t i;

    // Blit to LCD
    lcd_setCursor(row, 0);

    for (i = 0u; i < LCD_COLUMNS; i++)
    {
        if (buffer[i] != 0)
        {
            lcd_write((uint8_t)(buffer[i]));
        }
        else
        {
            break;
        }
    }

    // Make sure we blank out rest of line with spaces
    for (; i < LCD_COLUMNS; i++)
    {
        lcd_write(' ');
    }
}

static void writeAll(void)
{
    uint8_t i;
    char buffer[LCD_COLUMNS + 5]; // We want to have some extra space in the buffer

    // The LCD's four rows:
    //   row0: Menu title (always), menu_item = 0
    //   row1: First visible menu item, menu_item = 1, if MenuOffset = 0
    //   row2: Next  visible menu item, menu_item = 2, if MenuOffset = 0
    //   row3: Third visible menu item, menu_item = 3, if MenuOffset = 0

    // Now, if we have some offset:
    //   row1: menu_item = 2, if MenuOffset = 1

    // Cursor position refers to menu_item being pointed at

    if (menuHasStaticTitle(Menu))
    {
        // Title row is fixed
        memset(buffer, ' ', LCD_COLUMNS + 5);
        menuWriteItem(Menu, 0, buffer);
        writeBufferToLcd(0, buffer);
        i = 1;
    }
    else
    {
        i = 0;
    }

    // Menu items get indented by one space
    for (; i < LCD_ROWS; i++)
    {
        memset(buffer, ' ', LCD_COLUMNS + 5);
        menuWriteItem(Menu, i + MenuOffset, &(buffer[1]));
        writeBufferToLcd(i, buffer);
    }
}

static void writeMenuItem(uint8_t item)
{
    uint8_t row;
    uint8_t col;
    char buffer[LCD_COLUMNS + 5]; // We want to have some extra space in the buffer
    memset(buffer, ' ', LCD_COLUMNS + 5);

    // Determine where to draw this menu item
    if (menuHasStaticTitle(Menu) && (item == 0))
    {
        // Its a menu title
        row = 0;
        col = 0;
    }
    else
    {
        // Its a regular menu item, which is offset into display:
        row = item - MenuOffset;
        col = 1;
    }

    // Is this visible?
    if (row < LCD_ROWS)
    {
        // Let menu write up what it wants to display
        menuWriteItem(Menu, item, &(buffer[col]));
        writeBufferToLcd(row, buffer);
    }
}

static void drawCursor(void)
{
    uint8_t i;

    if (menuHasStaticTitle(Menu))
    {
        i = 1;
    }
    else
    {
        i = 0;
    }

    for (; i < LCD_ROWS; i++)
    {
        lcd_setCursor(i, 0);
        lcd_write((i == cursorRow) ? LCD_CHAR_RIGHTARROW : ' ');
    }

    // Set the visible cursor correctly
    lcd_setCursor(cursorRow, cursorCol);
}


// ---------------------------  PUBLIC FUNCTIONS  -------------------------------



// This will reset variables and display main menu
void ui_initialize(void)
{
    // Reset variables
    MenuOffset = 0;
    RequestUpdate = REQUEST_NONE;

    MenuParent = NULL;
    MenuParentParent = NULL;

    cursorCol = 0;
    cursorRow = 0;

    // We want main menu hooked up initially
    ui_menuEnter(&mainmenu_Menu);
}


void ui_handleUserEvent(uint8_t user_event)
{
    // Pass on user event to currently active menu

    if (Menu != NULL)
    {
        menuHandleUiEvent(Menu, user_event);
    }
    else
    {
        // TODO check this other places also
        err_raise(ERR_MODULE_UI, __LINE__);
    }
}


void ui_handleMainLoopHandler(void)
{
    if (RequestUpdate != REQUEST_NONE)
    {
        if (RequestUpdate == REQUEST_ALL)
        {
            writeAll();
        }
        else
        {
            writeMenuItem(RequestUpdate - REQUEST_FIRST_ITEM);
        }

        // Reset cursor
        drawCursor();

        RequestUpdate = REQUEST_NONE;
    }
}

void ui_requestUpdateAll(void)
{
    RequestUpdate = REQUEST_ALL;
}

void ui_requestUpdate(uint8_t menu_item)
{
    if (RequestUpdate != REQUEST_NONE)
    {
        RequestUpdate = REQUEST_ALL;
    }
    else
    {
        RequestUpdate = REQUEST_FIRST_ITEM + menu_item;
    }
}

const menuInterface_t * ui_getCurrentMenu(void)
{
    return Menu;
}


// When entering a menu, ui_menuEnter must be called with the new menu manifest.
// This will make ui render the menu.
void ui_menuEnter(const menuInterface_t *menu)
{
    // Store pointer to menu, keeping two parents

    if (MenuParentParent != NULL)
    {
        // We are nesting too deep!
        err_raise(ERR_MODULE_UI, __LINE__);
    }

    MenuParentParent = MenuParent;
    MenuParent = Menu;
    Menu = menu;

    // Set an off-limits menu offset, and get new menu's default cursor
    MenuOffset = -1;

    // MoveCursor function will fix everything and redraw current view now
    // TODO this should be deferred to an update call
    ui_menuMoveCursor(menuInitGetCursor(Menu), 0);
}

// Leave current menu. Let parent menu get in focus
void ui_menuBackOut(void)
{
    // Store pointer to menu, keeping two parents
    Menu = MenuParent;
    MenuParent = MenuParentParent;
    MenuParentParent = NULL;

    // Set am off-limits menu offset, and get new menu's default cursor
    MenuOffset = -1;

    // MoveCursor function will fix everything anMenuCursorItemd redraw current view now
    ui_menuMoveCursor(menuInitGetCursor(Menu), 0);
}

// Make sure cursorItem is visible, and place cursor correctly
void ui_menuMoveCursor(uint8_t cursorItem, uint8_t cursorIndent)
{
    uint8_t itemCount;
    bool_t needRedraw = FALSE;

    // Get number of items
    itemCount = menuGetItemCount(Menu);

    // Bounds check cursor position
    if (cursorItem >= itemCount)
    {
        cursorItem = itemCount - 1;
    }
    else if (((int8_t)cursorItem) < 0)
    {
        cursorItem = 0;
    }

    // Load desired cursor position

    // Is MenuOffset in range?
    if (MenuOffset < 0)
    {
        MenuOffset = 0;
        needRedraw = TRUE;
    }

    // Is cursorItem visible?

    if (menuHasStaticTitle(Menu))
    {
        if (cursorItem < (MenuOffset+1))
        {
            // We must move offset
            needRedraw = TRUE;
            MenuOffset = cursorItem - 1;
        }
        else if (cursorItem > (MenuOffset + 3))
        {
            needRedraw = TRUE;
            MenuOffset = cursorItem - 3;
        }
    }
    else
    {
        if (cursorItem < MenuOffset)
        {
            // We must move offset
            needRedraw = TRUE;
            MenuOffset = cursorItem;
        }
        else if (cursorItem > (MenuOffset + 3))
        {
            needRedraw = TRUE;
            MenuOffset = cursorItem - 3;
        }
    }

    if (needRedraw)
    {
        writeAll();

        // If we have redrawn everything, we can clear any pending request
        RequestUpdate = REQUEST_NONE;
    }

    cursorCol = cursorIndent;
    cursorRow = cursorItem - MenuOffset;

    drawCursor();
}

int8_t ui_eventToDelta(uint8_t ui_event, int8_t fast_speed)
{
    int8_t delta = 0;

    switch (ui_event)
    {
    case UI_EVENT_MOVE_UP:
        delta = 1;
        break;
    case UI_EVENT_MOVE_DOWN:
        delta = -1;
        break;
    case UI_EVENT_MOVE_UP | UI_MOVE_FAST_MASK:
        delta = fast_speed;
        break;

    case UI_EVENT_MOVE_DOWN | UI_MOVE_FAST_MASK:
        delta = -fast_speed;
        break;
    }

    return delta;
}

uint8_t ui_eventToSetClearBit(uint8_t ui_event, uint8_t x, uint8_t mask)
{
    uint8_t ret;

    switch (ui_event)
    {
    case UI_EVENT_MOVE_UP:
    case UI_EVENT_MOVE_UP | UI_MOVE_FAST_MASK:
        ret = x | mask;
        break;

    case UI_EVENT_MOVE_DOWN | UI_MOVE_FAST_MASK:
    case UI_EVENT_MOVE_DOWN:
        ret = x & ~mask;
        break;

    default:
        ret = x;
        break;
    }

    return ret;
}
